dslmande/arp3620-woodcase/production/dxf/ARP3620_Woodcase_Rev0.1_filler.dxf

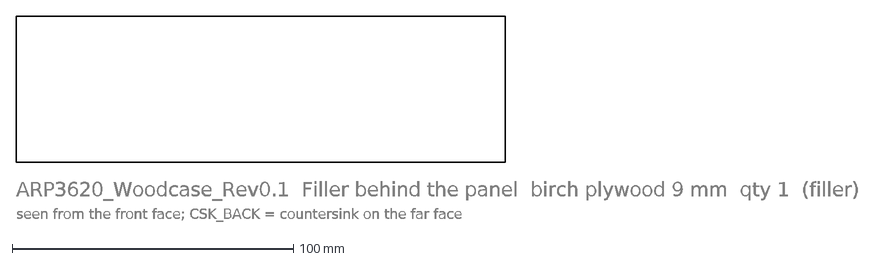
[picture p18: CAD file, 2026-10-08]
production/dxf/ARP3620_Woodcase_Rev0.1_filler.dxf
ARP3620_Woodcase_Rev0.1 Filler behind the panel birch plywood 9 mm qty 1 (filler)
seen from the front face; CSK_BACK = countersink on the far face
